arkadiraf/Juggling_Balls_Public/Images/20150408_191932.jpg

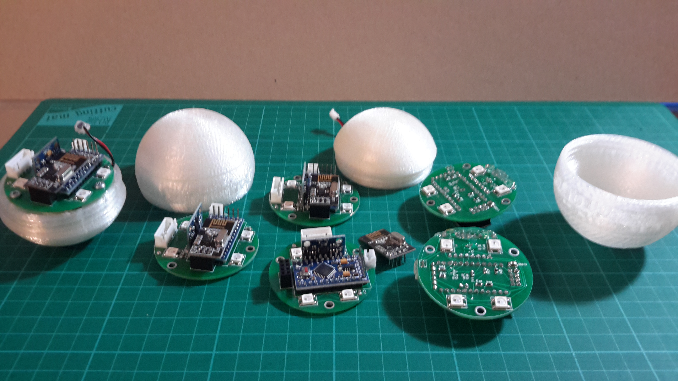
Images/20150408_191932.jpg
