arkadiraf/Juggling_Balls_Public/Images/Acc_Catch.png

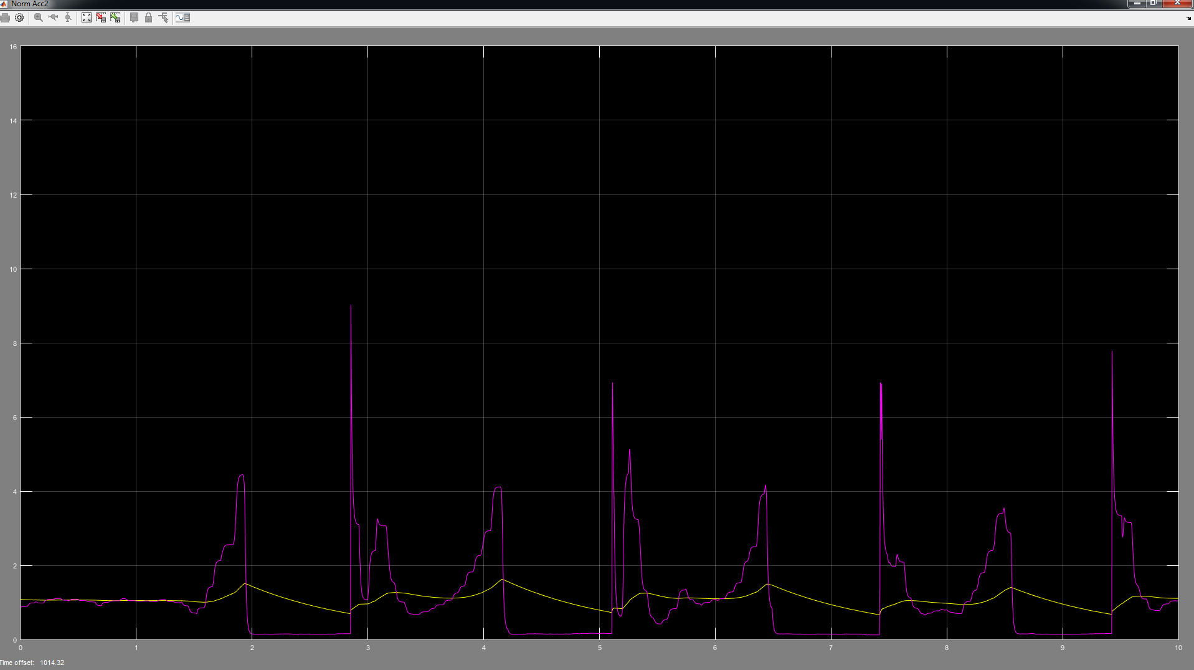
Images/Acc_Catch.png
