arkadiraf/Juggling_Balls_Public/Images/Acc_Catch_comment.png

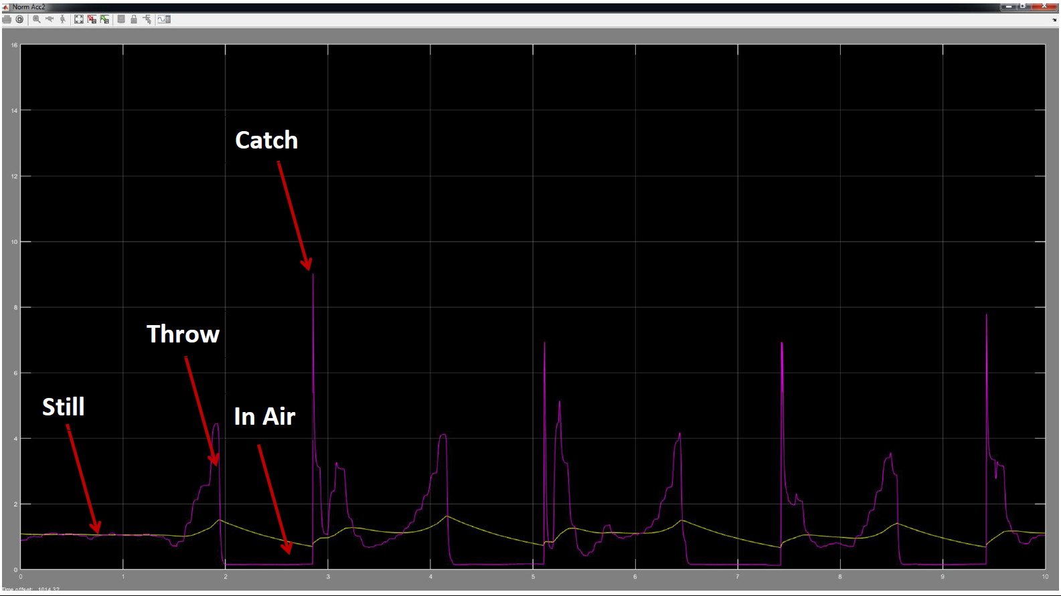
Images/Acc_Catch_comment.png
