arkadiraf/Juggling_Balls_Public/Images/Battery.jpg

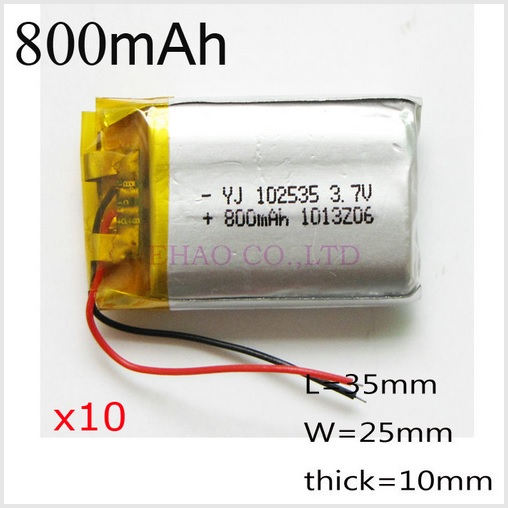
Images/Battery.jpg
