arkadiraf/Juggling_Balls_Public/Images/centrifugal force.jpg

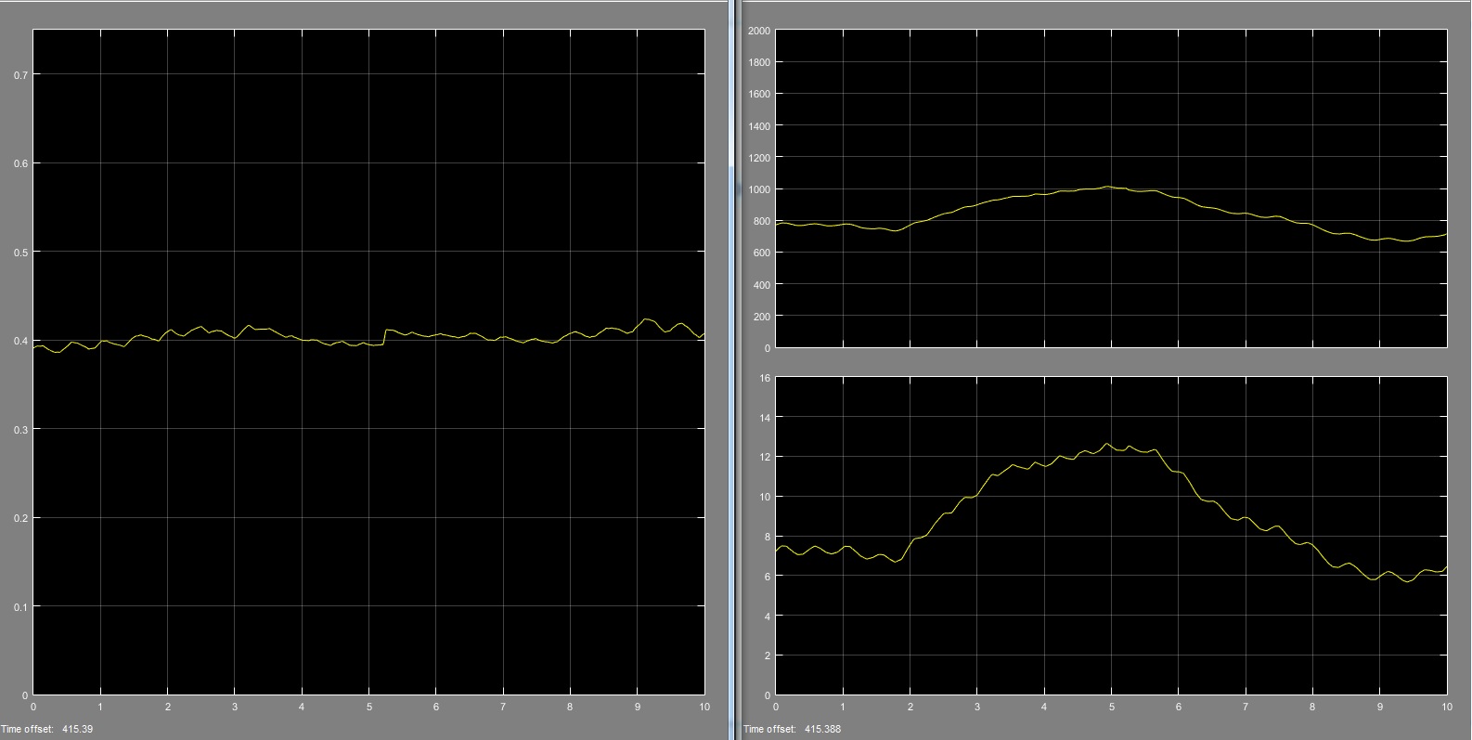
Images/centrifugal force.jpg
