arkadiraf/Juggling_Balls_Public/Images/ReedSwitch.JPG

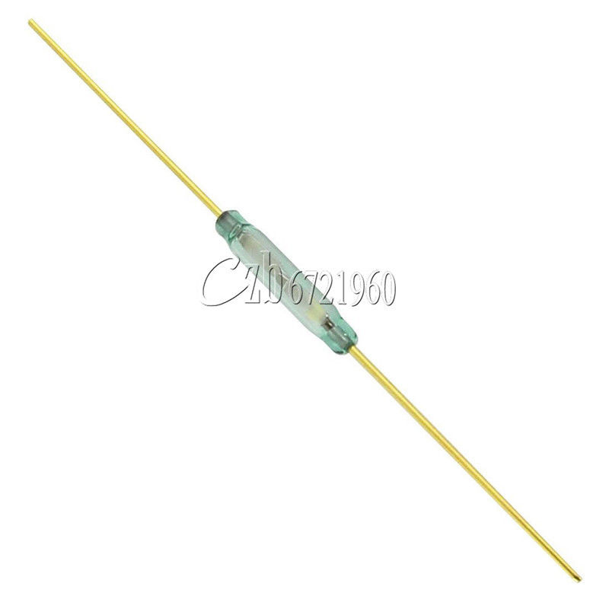
Images/ReedSwitch.JPG
